majkrzak/kropelka/firmware/cc1101.h

/** Low level interface for CC1101.
 */

#pragma once

#include <stddef.h>
#include <stdint.h>

/*! CC1101 Command Strobes.
 *  Defined in table 42 of cc1101 specs.
 */
enum cc1101_command_strobes {
  CC1101_SRES = 0x30,    //!<  Reset chip.
  CC1101_SFSTXON = 0x31, //!<  Enable and calibrate frequency synthesizer
  CC1101_SXOFF = 0x32,   //!<  Turn off crystal oscillator.
  CC1101_SCAL = 0x33,    //!<  Calibrate frequency synthesizer and turn it off.
  CC1101_SRX = 0x34,     //!<  Enable RX.
  CC1101_STX = 0x35,     //!<  Enable TX.
  CC1101_SIDLE = 0x36,   //!<  Exit RX / TX
  CC1101_SWOR = 0x38,    //!<  Start automatic RX polling sequence
  CC1101_SPWD = 0x39,    //!<  Enter power down mode when CSn goes high.
  CC1101_SFRX = 0x3A,    //!<  Flush the RX FIFO buffer.
  CC1101_SFTX = 0x3B,    //!<  Flush the TX FIFO buffer.
  CC1101_SWORRST = 0x3C, //!<  Reset real time clock to Event1 value.
  CC1101_SNOP = 0x3D,    //!<  No operation.
};

/*! CC1101 Configuration Registers.
 *  Defined in table 43 of cc1101 specs.
 */
enum cc1101_configuration_registers {
  CC1101_IOCFG2 = 0x00,   //!< GDO2 output pin configuration
  CC1101_IOCFG1 = 0x01,   //!< GDO1 output pin configuration
  CC1101_IOCFG0 = 0x02,   //!< GDO0 output pin configuration
  CC1101_FIFOTHR = 0x03,  //!< RX FIFO and TX FIFO thresholds
  CC1101_SYNC1 = 0x04,    //!< Sync word, high byte
  CC1101_SYNC0 = 0x05,    //!< Sync word, low byte
  CC1101_PKTLEN = 0x06,   //!< Packet length
  CC1101_PKTCTRL1 = 0x07, //!< Packet automation control
  CC1101_PKTCTRL0 = 0x08, //!< Packet automation control
  CC1101_ADDR = 0x09,     //!< Device address
  CC1101_CHANNR = 0x0A,   //!< Channel number
  CC1101_FSCTRL1 = 0x0B,  //!< Frequency synthesizer control
  CC1101_FSCTRL0 = 0x0C,  //!< Frequency synthesizer control
  CC1101_FREQ2 = 0x0D,    //!< Frequency control word, high byte
  CC1101_FREQ1 = 0x0E,    //!< Frequency control word, middle byte
  CC1101_FREQ0 = 0x0F,    //!< Frequency control word, low byte
  CC1101_MDMCFG4 = 0x10,  //!< Modem configuration
  CC1101_MDMCFG3 = 0x11,  //!< Modem configuration
  CC1101_MDMCFG2 = 0x12,  //!< Modem configuration
  CC1101_MDMCFG1 = 0x13,  //!< Modem configuration
  CC1101_MDMCFG0 = 0x14,  //!< Modem configuration
  CC1101_DEVIATN = 0x15,  //!< Modem deviation setting
  CC1101_MCSM2 = 0x16,    //!< Main Radio Control State Machine configuration
  CC1101_MCSM1 = 0x17,    //!< Main Radio Control State Machine configuration
  CC1101_MCSM0 = 0x18,    //!< Main Radio Control State Machine configuration
  CC1101_FOCCFG = 0x19,   //!< Frequency Offset Compensation configuration
  CC1101_BSCFG = 0x1A,    //!< Bit Synchronization configuration
  CC1101_AGCTRL2 = 0x1B,  //!< AGC control
  CC1101_AGCTRL1 = 0x1C,  //!< AGC control
  CC1101_AGCTRL0 = 0x1D,  //!< AGC control
  CC1101_WOREVT1 = 0x1E,  //!< High byte Event 0 timeout
  CC1101_WOREVT0 = 0x1F,  //!< Low byte Event 0 timeout
  CC1101_WORCTRL = 0x20,  //!< Wake On Radio control
  CC1101_FREND1 = 0x21,   //!< Front end RX configuration
  CC1101_FREND0 = 0x22,   //!< Front end TX configuration
  CC1101_FSCAL3 = 0x23,   //!< Frequency synthesizer calibration
  CC1101_FSCAL2 = 0x24,   //!< Frequency synthesizer calibration
  CC1101_FSCAL1 = 0x25,   //!< Frequency synthesizer calibration
  CC1101_FSCAL0 = 0x26,   //!< Frequency synthesizer calibration
  CC1101_RCCTRL1 = 0x27,  //!< RC oscillator configuration
  CC1101_RCCTRL0 = 0x28,  //!< RC oscillator configuration
  CC1101_FSTEST = 0x29,   //!< Frequency synthesizer calibration control
  CC1101_PTEST = 0x2A,    //!< Production test
  CC1101_AGCTEST = 0x2B,  //!< AGC test
  CC1101_TEST2 = 0x2C,    //!< Various test settings
  CC1101_TEST1 = 0x2D,    //!< Various test settings
  CC1101_TEST0 = 0x2E,    //!< Various test settings
};

/*! CC1101 Status Registers.
 *  Defined in table 44 of cc1101 specs.
 *  Can be accesed only through the burst read.
 */
enum cc1101_status_registers {
  CC1101_PARTNUM = 0x30,    //!< Part number for CC1101
  CC1101_VERSION = 0x31,    //!< Current version number
  CC1101_FREQEST = 0x32,    //!< Frequency Offset Estimate
  CC1101_LQI = 0x33,        //!< Demodulator estimate for Link Quality
  CC1101_RSSI = 0x34,       //!< Received signal strength indication
  CC1101_MARCSTATE = 0x35,  //!< Control state machine state
  CC1101_WORTIME1 = 0x36,   //!< High byte of WOR timer
  CC1101_WORTIME0 = 0x37,   //!< Low byte of WOR timer
  CC1101_PKTSTATUS = 0x38,  //!< Current GDOx status and packet status
  CC1101_VCO_VC_DAC = 0x39, //!< Current setting from PLL calibration module
  CC1101_TXBYTES = 0x3A,    //!< Underflow and number of bytes in the TX FIFO
  CC1101_RXBYTES = 0x3B,    //!< Overflow and number of bytes in the RX FIFO
  CC1101_RCCTRL1_STATUS = 0x3C, //!< Last RC oscillator calibration result
  CC1101_RCCTRL0_STATUS = 0x3D, //!< Last RC oscillator calibration result
};

/*! CC1101 Burst Registers
 *  Special registers which can only be accesed through the burst read/write
 * (TX/RX FIFO, PATABLE), or usualy are (SYNC, FREQ, ...).
 */
enum cc1101_burst_registers {
  CC1101_IOCFG = 0x00,   //!< GDO2 output pin configuration (3 bytes)
  CC1101_SYNC = 0x04,    //!< Sync word (2 bytes)
  CC1101_PKTCTRL = 0x07, //!< Packet automation control (2 bytes)
  CC1101_FSCTRL = 0x0B,  //!< Frequency synthesizer control (2 bytes)
  CC1101_FREQ = 0x0D,    //!< Frequency control word (3 bytes)
  CC1101_MDMCFG = 0x10,  //!< Modem configuration (5 bytes)
  CC1101_MCSM = 0x16,    //!< State Machine configuration (3 bytes)
  CC1101_AGCTRL = 0x1B,  //!< AGC control (3 bytes)
  CC1101_WOREVT = 0x1E,  //!< Event 0 timeout (2 bytes)
  CC1101_FREND = 0x21,   //!< Front end configuration (2 bytes)
  CC1101_FSCAL = 0x23,   //!< Frequency synthesizer calibration (4 bytes)
  CC1101_RCCTRL = 0x27,  //!< RC oscillator configuration (2 bytes)
  CC1101_TEST = 0x2C,    //!< Various test settings (3 bytes)
  CC1101_PATABLE = 0x3E, //!< PA control settings (8 bytes)
  CC1101_FIFO = 0x3F,    //!< TX/RX FIFO (64 bytes)
};

void cc1101_init();
uint8_t cc1101_strobe(uint8_t);
uint8_t cc1101_write(uint8_t, uint8_t);
uint8_t cc1101_burst_write(uint8_t, uint8_t *, size_t);
